RobieElliz/esp32InductanceMeterV2/Photos/KiCad PCB Photos/Back PCB Layout.png

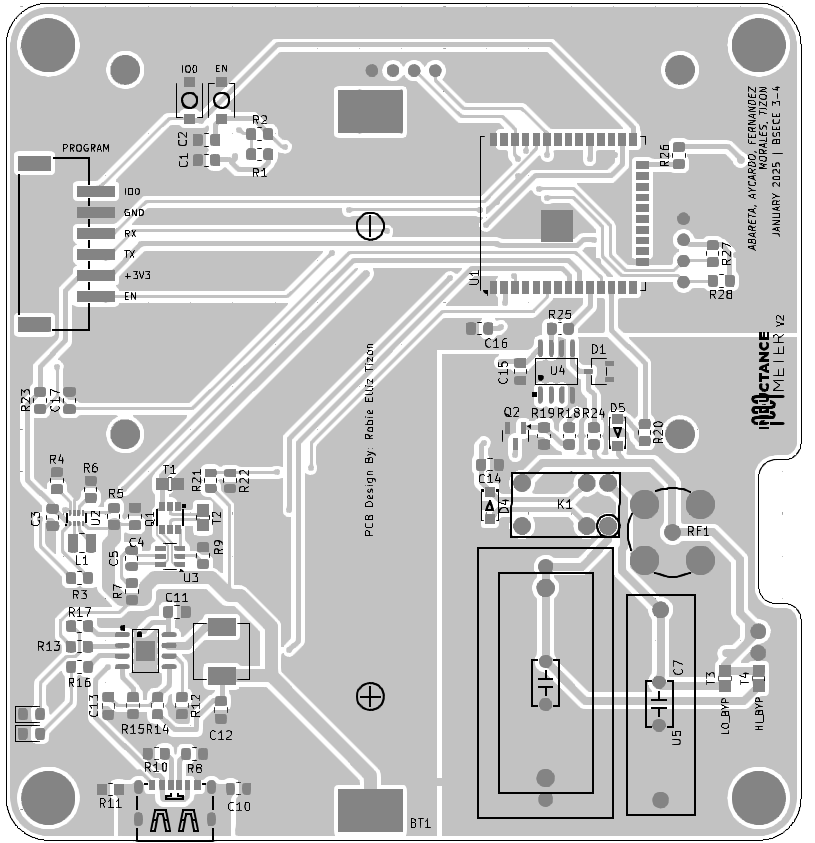
Photos/KiCad PCB Photos/Back PCB Layout.png
