RobieElliz/esp32InductanceMeterV2/Photos/Overall Photos/IMG_5033.jpg

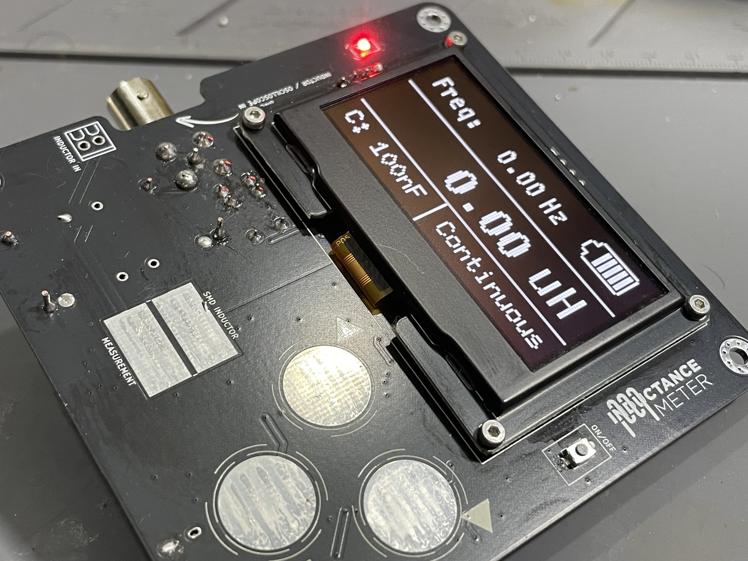
Photos/Overall Photos/IMG_5033.jpg
