RobieElliz/esp32InductanceMeterV2/Photos/Overall Photos/IMG_5036.jpg

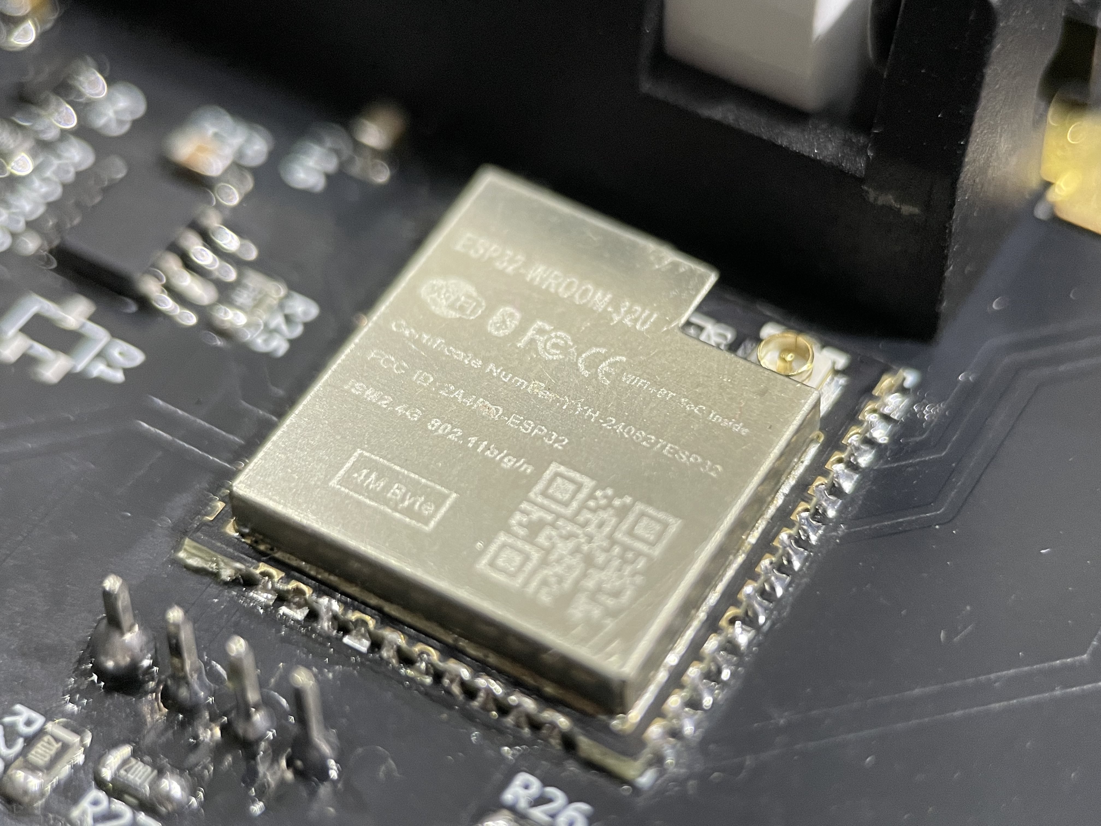
Photos/Overall Photos/IMG_5036.jpg
