RobieElliz/esp32InductanceMeterV2/Photos/Overall Photos/IMG_5037.jpg

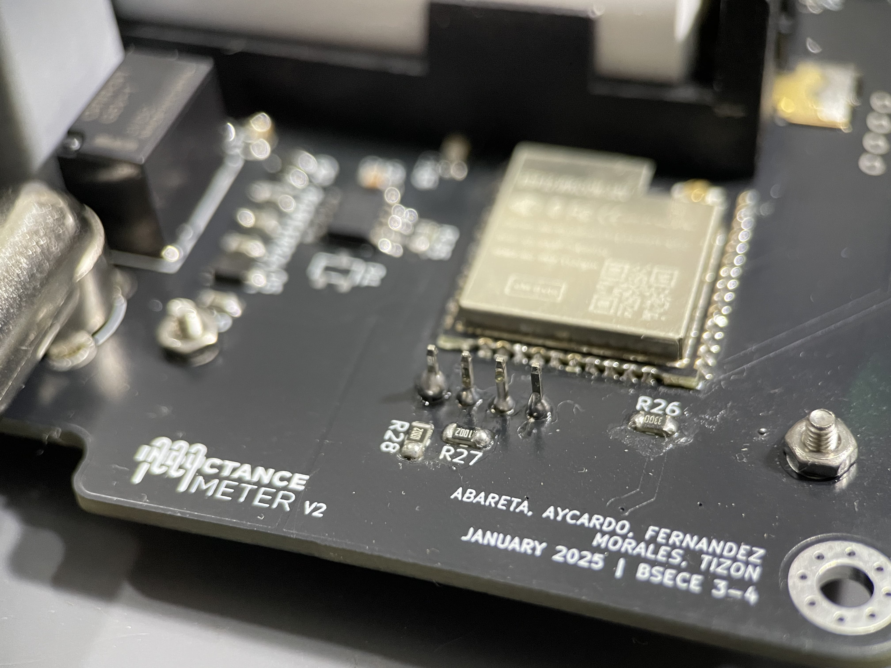
Photos/Overall Photos/IMG_5037.jpg
