RobieElliz/esp32InductanceMeterV2/Photos/Overall Photos/IMG_5038.jpg

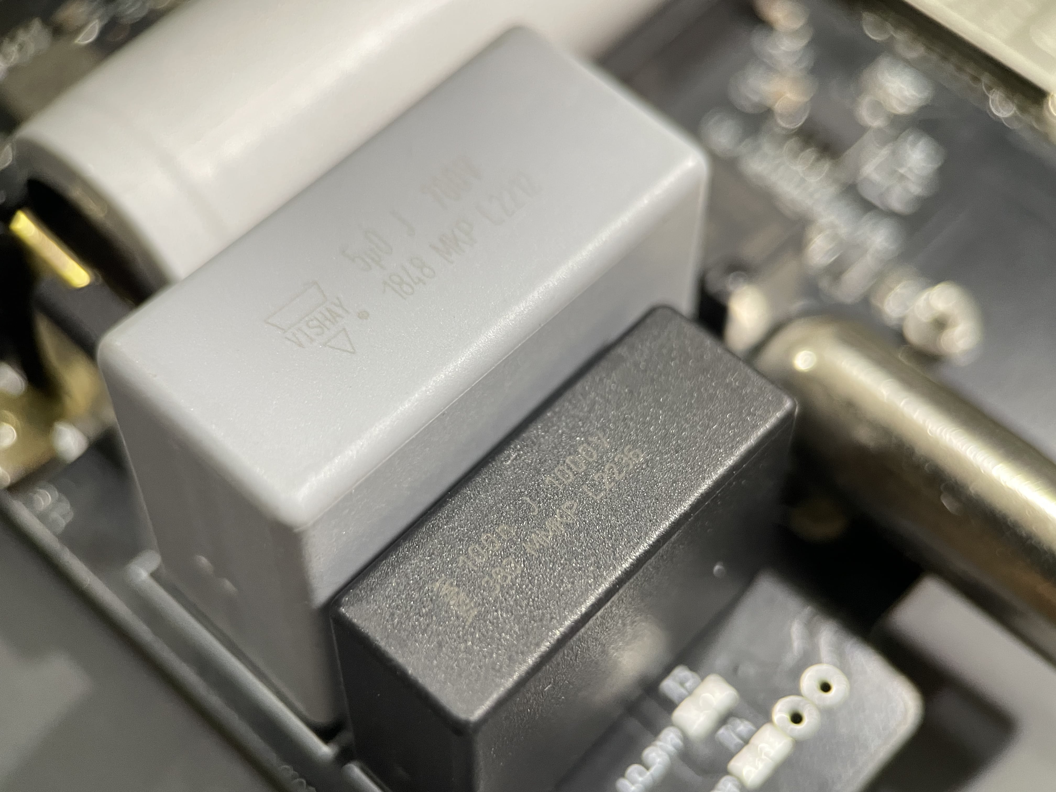
Photos/Overall Photos/IMG_5038.jpg
