RobieElliz/esp32InductanceMeterV2/Photos/Overall Photos/IMG_5039.jpg

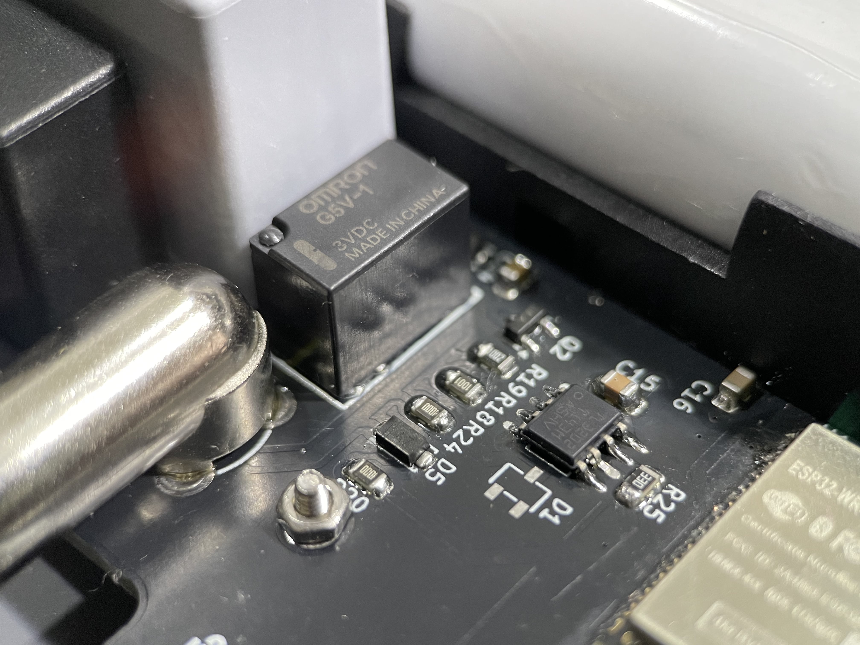
Photos/Overall Photos/IMG_5039.jpg
