RobieElliz/esp32InductanceMeterV2/Photos/Overall Photos/IMG_5040.jpg

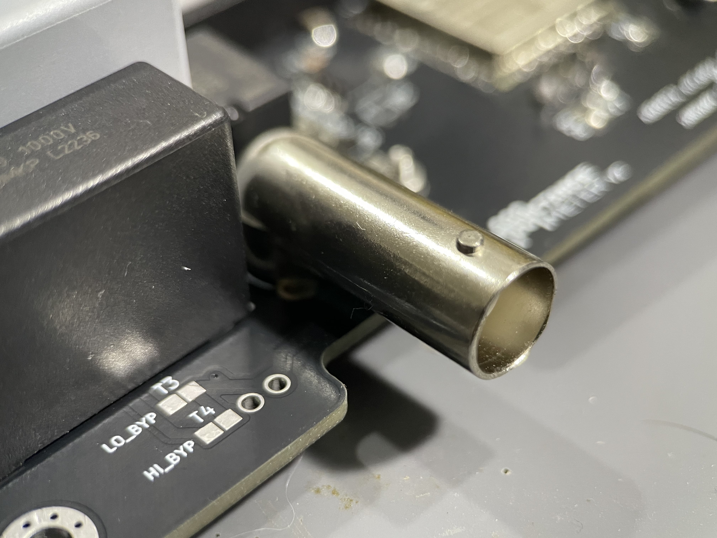
Photos/Overall Photos/IMG_5040.jpg
