RobieElliz/esp32InductanceMeterV2/Photos/Overall Photos/IMG_5042.jpg

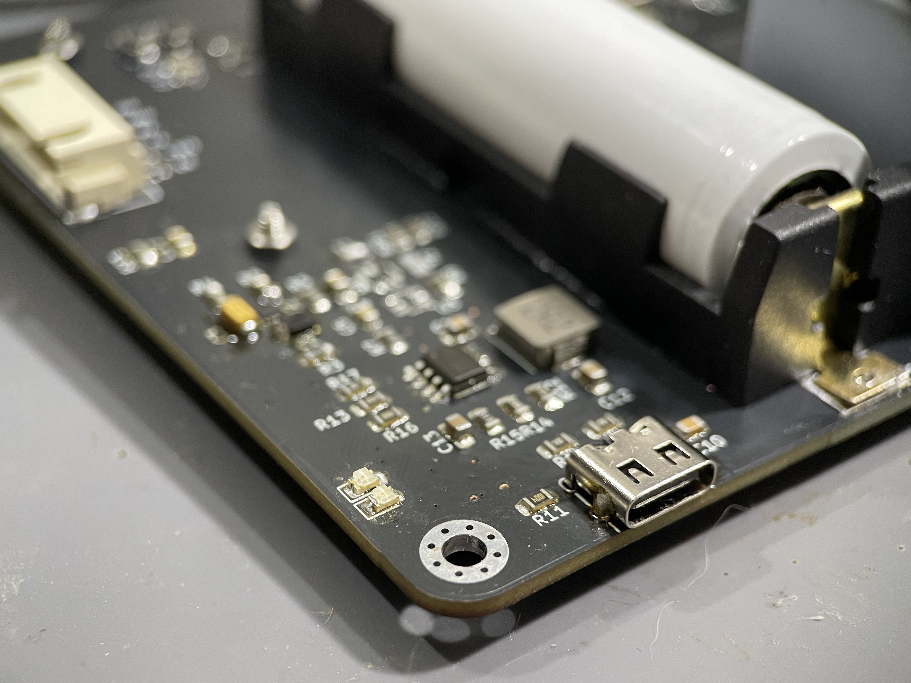
Photos/Overall Photos/IMG_5042.jpg
